makingdevices/StopWatch/v1/PowerProfile/AllScreenON_Counting.png

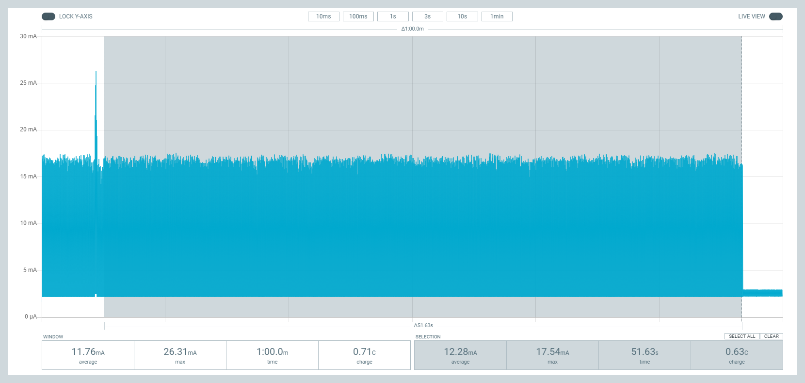
v1/PowerProfile/AllScreenON_Counting.png
